joshellissh/PiDGC/source/display/images/left_gauge_bg.png

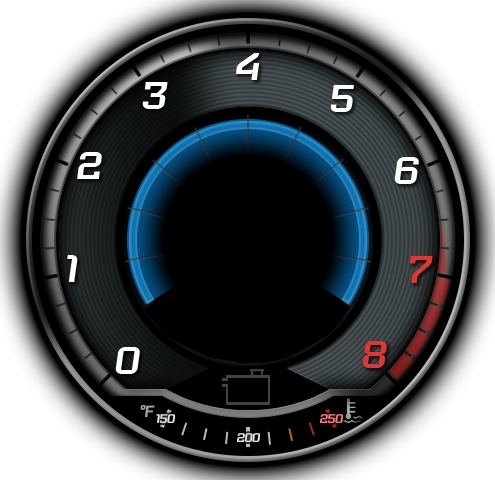
source/display/images/left_gauge_bg.png
