joshellissh/PiDGC/source/display/images/center_lines.png

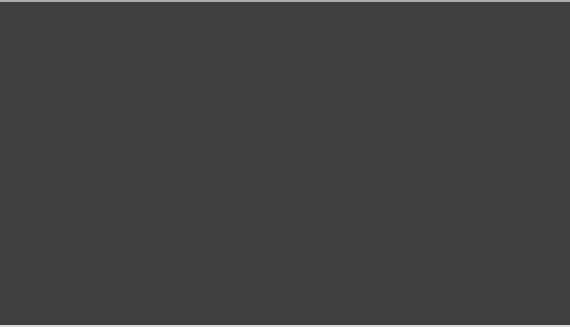
source/display/images/center_lines.png
