joshellissh/PiDGC/source/display/images/left_gauge_fg.png

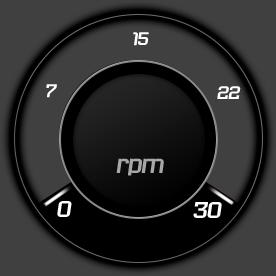
source/display/images/left_gauge_fg.png
