joshellissh/PiDGC/source/display/mainwindow.h

#ifndef MAINWINDOW_H
#define MAINWINDOW_H

#include <QMainWindow>
#include <QKeyEvent>

class MainWindow : public QMainWindow
{
    Q_OBJECT

public:
    MainWindow(QWidget *parent = 0);
    ~MainWindow();
    void keyPressEvent(QKeyEvent *event);
};

#endif // MAINWINDOW_H
