joshellissh/PiDGC/source/microcontroller/pins.h

#ifndef PINS_H
#define PINS_H

#define BUZZER          2
#define FUEL_LEVEL      A6
#define GAUGE_LIGHTS    5
#define HIGH_BEAMS      6
#define HPL_INPUT       16
#define HPL_LED         15
#define LEFT_BLINKER    7
#define LOW_BEAMS       8
#define MIL             9
#define RIGHT_BLINKER   11
#define VOLTAGE         A5
#define VSS             12

#endif
