joshellissh/PiDGC/source/display/window.h

#ifndef WINDOW_H
#define WINDOW_H

#include "painter.h"
#include <QWidget>
#include "glwidget.h"
#include <QLabel>
#include <QGridLayout>
#include <QKeyEvent>
#include "hwdialog.h"

class Window : public QWidget
{
    Q_OBJECT

public:
    Window(VehicleValues &vehicle, Indicators &indicators);
    void keyPressEvent(QKeyEvent *event);
    void mousePressEvent(QMouseEvent *event);
    void setHWDialog(HWDialog &hwDialog);

private:
    Painter *painter;
    VehicleValues *vehicle;
    Indicators *indicators;
    HWDialog *hwDialog;
};

#endif // WINDOW_H
