joshellissh/PiDGC/source/microcontroller/globals.h

#ifndef GLOBALS_H
#define GLOBALS_H

#include "sdcard.h"
#include "values.h"
#include "canbus.h"
#include "indicators.h"

extern SDCard sdCard;
extern Values values;
extern Canbus canbus;
extern Indicators indicators;
extern BuzzerSound milSound;

#endif
