joshellissh/PiDGC/source/display/variables.h

#ifndef VARIABLES_H
#define VARIABLES_H

#include "vehiclevalues.h"
#include "indicators.h"

#define SCREEN_WIDTH        1280.0f
#define HALF_SCREEN_WIDTH   (SCREEN_WIDTH / 2.0f)
#define SCREEN_HEIGHT       480.0f
#define HALF_SCREEN_HEIGHT  (SCREEN_HEIGHT / 2.0f)

#define MAX_RPM             8000.0f
#define MAX_MPH             160.0f
#define MAX_BOOST           30.0f

#endif // VARIABLES_H
