joshellissh/PiDGC/source/uc-sim/values.h

#ifndef VEHICLEVALUES_H
#define VEHICLEVALUES_H

class Values {
public:
  float boostPressure;
  int coolantTemp;
  float fuelLevel;
  bool gaugeLights;
  bool highBeams;
  bool leftBlinker;
  bool lowBeams;
  bool mil;
  int mph;
  float oilPressure;
  float odometer;
  bool reverse;
  bool rightBlinker;
  int rpm;
  float tripOdometer;
  float voltage;
};

#endif
